klavatron/esp8266-weather/pcbs/breadboard/meteo_fritzing_sketch_bb.jpg

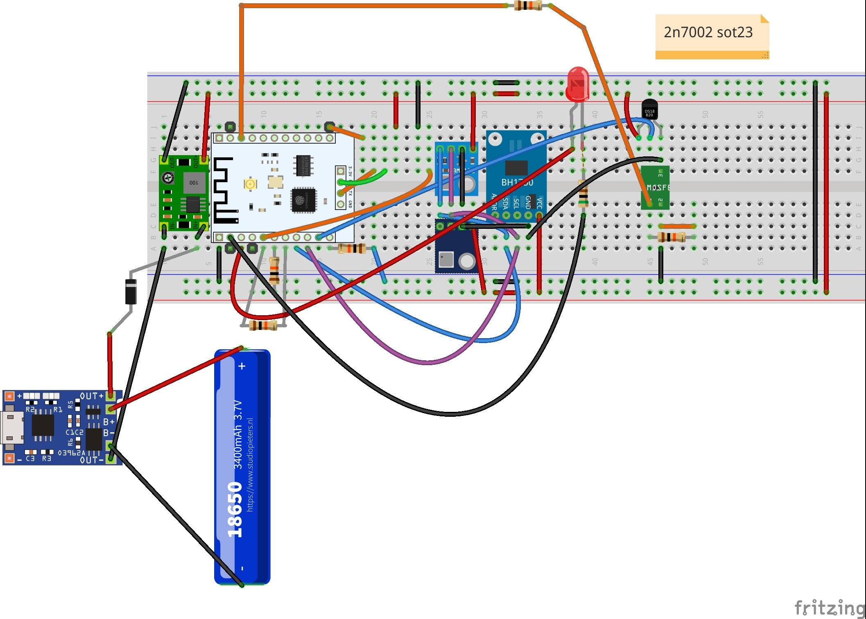
pcbs/breadboard/meteo_fritzing_sketch_bb.jpg
