klavatron/esp8266-weather/pcbs/esp201/2.jpg

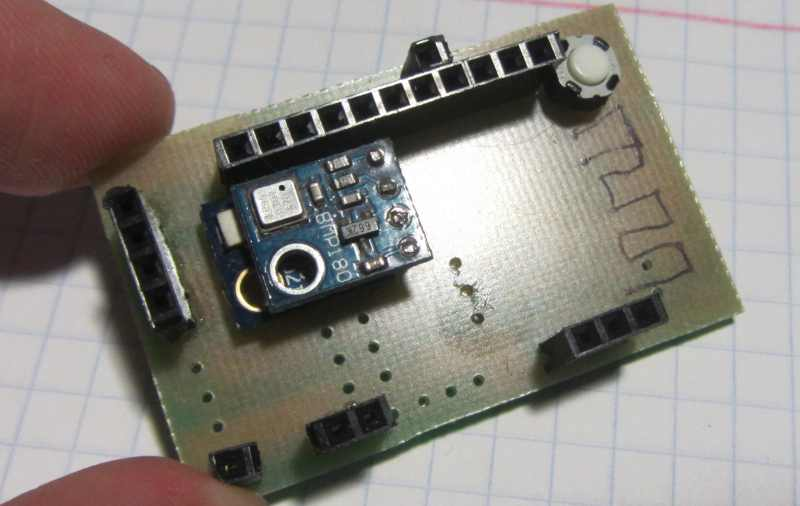
pcbs/esp201/2.jpg
