klavatron/esp8266-weather/pcbs/esp201/3.jpg

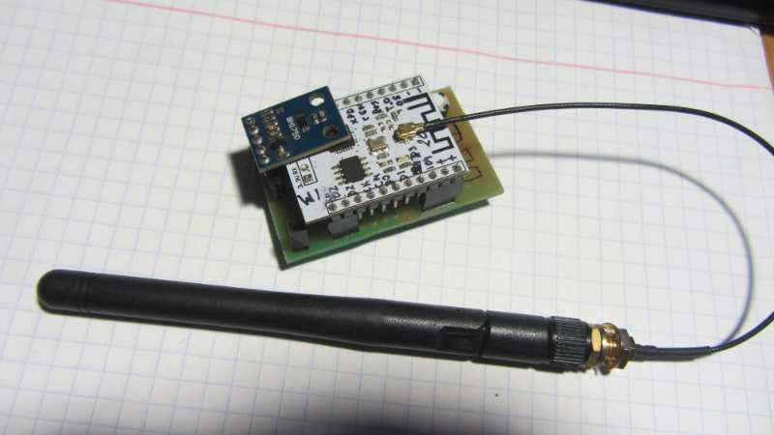
pcbs/esp201/3.jpg
