klavatron/esp8266-weather/pcbs/esp201/weather2.jpg

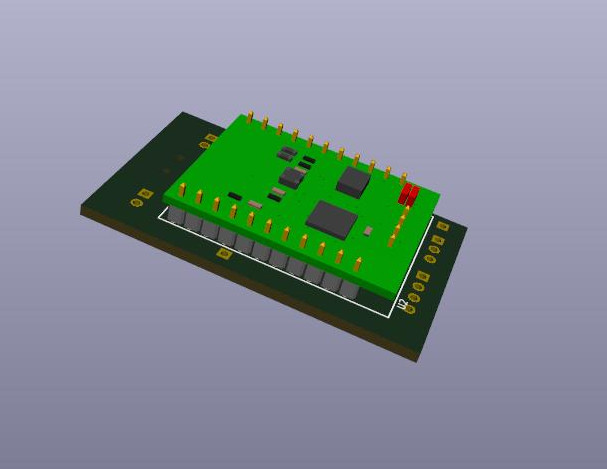
pcbs/esp201/weather2.jpg
