klavatron/esp8266-weather/pcbs/esp8266-12f-analog_multiplexer/weather_mux.jpg

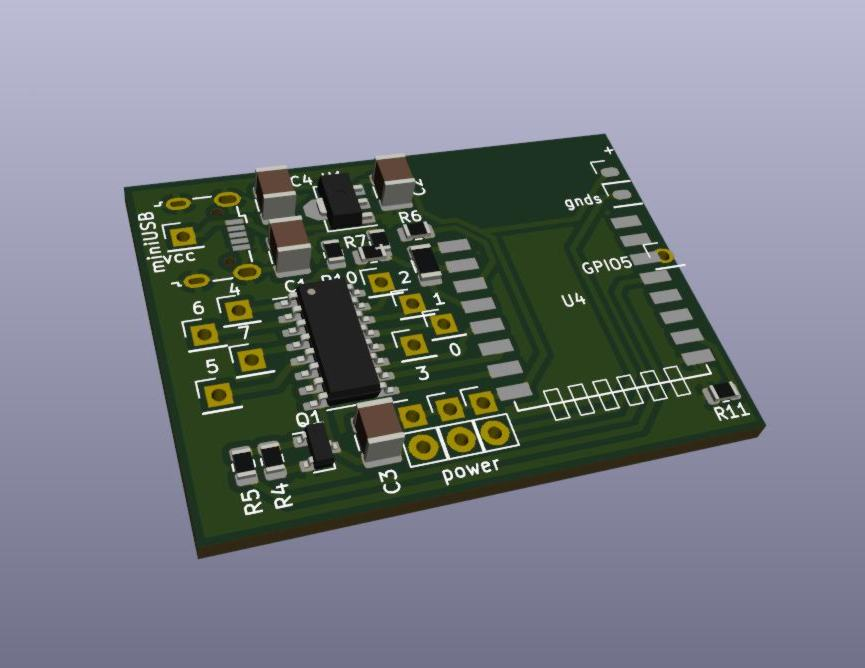
pcbs/esp8266-12f-analog_multiplexer/weather_mux.jpg
